codingABI/TransistorTesterSH1106Perfboard/Schematic/TransistorTesterSH1106Perfboard.kicad_sch

## KiCad design Schematic/TransistorTesterSH1106Perfboard.kicad_sch (2026-03-06)

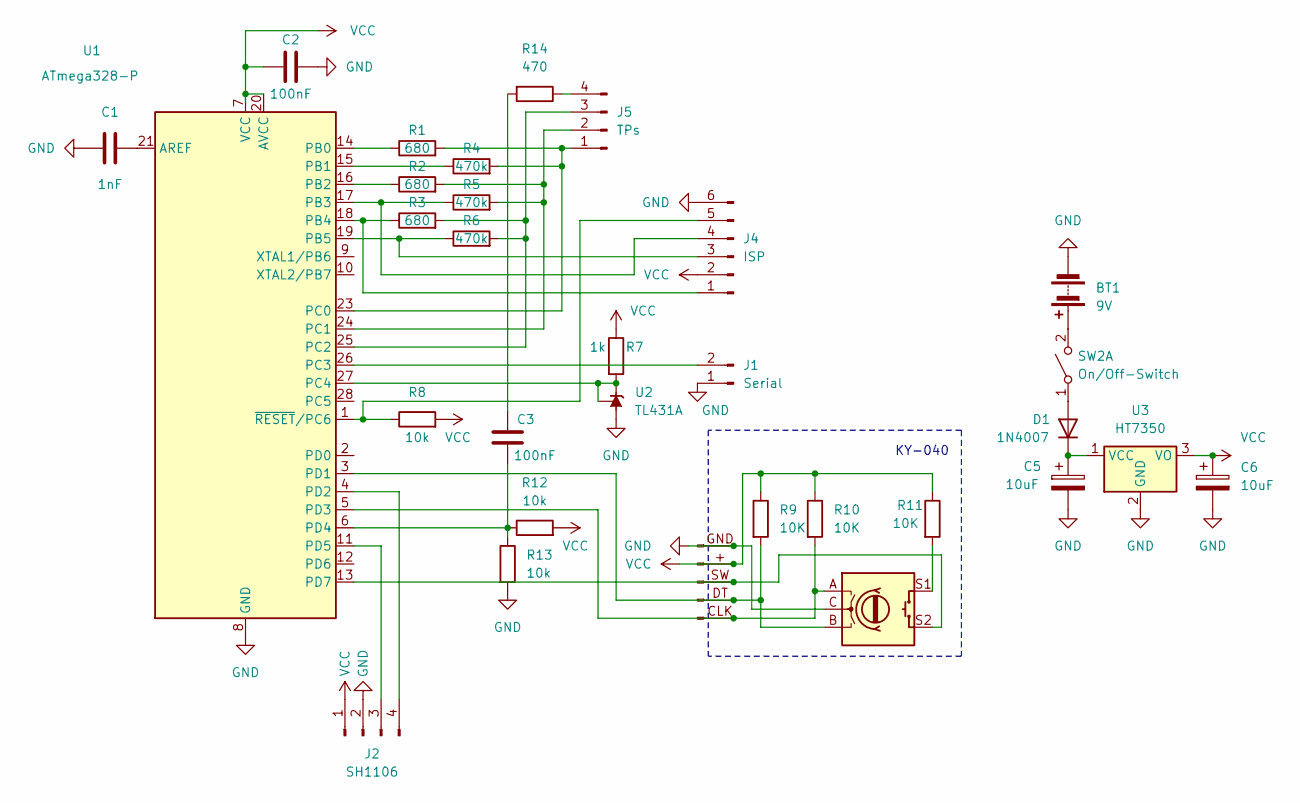
[picture p10: schematic TransistorTesterSH1106Perfboard.kicad_sch]

Parts:
BT1: 9V
C1: 1nF
C2, C3: 100nF
C5, C6: 10uF
D1: 1N4007
J1: Serial
J2: SH1106
J3: Conn_01x05_Male
J4: ISP
J5: TPs
R1, R2, R3: 680
R4, R5, R6: 470k
R7: 1k
R8, R12, R13: 10k
R9, R10, R11: 10K; R_Axial_DIN0207_L6.3mm_D2.5mm_P10.16mm_Horizontal
R14: 470
SW1: RotaryEncoder_Switch
SW2: On/Off-Switch
U1: ATmega328-P; DIP-28_W7.62mm
U2: TL431A; TO-92_Inline
U3: HT7350; TO-252-2

Connections:
GND: BT1.2 (-), C1.1, C2.2, C5.2, C6.2, J1.1, J2.2, J3.GND (Pin_1), J4.6, R13.2, SW1.C, U1.8 (GND), U1.22 (GND), U2.2 (A), U3.2 (GND)
unnamed: BT1.1 (+), SW2.2 (B)
unnamed: C1.2, U1.21 (AREF)
unnamed: C3.1, R14.2
unnamed: C3.2, R12.1, R13.1, U1.6 (PD4)
unnamed: C5.1, D1.1 (K), U3.1 (VCC)
unnamed: D1.2 (A), SW2.1 (A)
unnamed: J1.2, U1.26 (PC3)
unnamed: J2.3, U1.11 (PD5)
unnamed: J2.4, U1.4 (PD2)
unnamed: J3.CLK (Pin_5), R10.2, SW1.A, U1.5 (PD3)
unnamed: J3.DT (Pin_4), R9.2, SW1.B, U1.3 (PD1)
unnamed: J3.SW (Pin_3), SW1.S2, U1.13 (PD7)
unnamed: J4.1, R3.1, U1.18 (PB4)
unnamed: J4.3, R6.1, U1.19 (PB5)
unnamed: J4.4, R5.1, U1.17 (PB3)
unnamed: J4.5, R8.1, U1.1 (~RESET/PC6)
unnamed: J5.1, R1.2, R4.2, U1.23 (PC0)
unnamed: J5.2, R2.2, R5.2, U1.24 (PC1)
unnamed: J5.3, R3.2, R6.2, U1.25 (PC2)
unnamed: J5.4, R14.1
unnamed: R1.1, U1.14 (PB0)
unnamed: R2.1, U1.16 (PB2)
unnamed: R4.1, U1.15 (PB1)
unnamed: R7.2, U1.27 (PC4), U2.1 (REF), U2.3 (K)
unnamed: R11.2, SW1.S1
VCC: C2.1, C6.1, J2.1, J3.+ (Pin_2), J4.2, R7.1, R8.2, R9.1, R10.1, R11.1, R12.2, U1.7 (VCC), U1.20 (AVCC), U3.3 (VO)

Notes on the sheet:
KY-040
